makespacemadrid/cheap-wled-controller/images/ch224k_pin_description.png

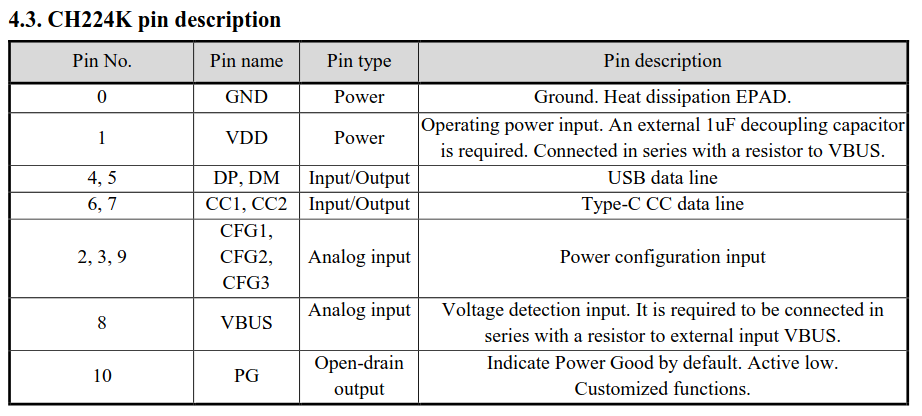
images/ch224k_pin_description.png
